Natchpai/BeyondCMoy/Beyond_CMoy/Images/Components/RK097GS.png

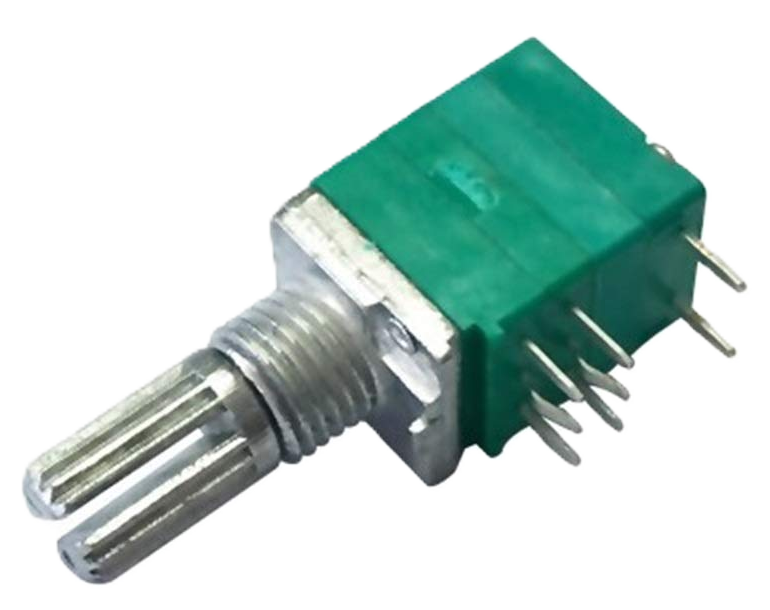
Beyond_CMoy/Images/Components/RK097GS.png
