Natchpai/BeyondCMoy/Beyond_CMoy/Images/Components/TYPEC6P019.jpg

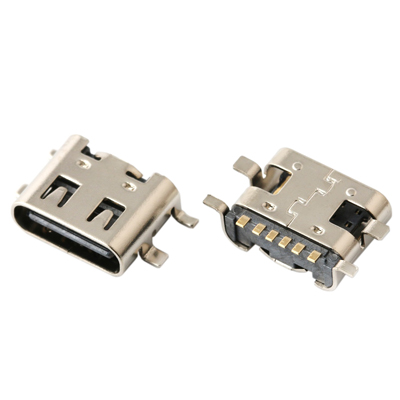
Beyond_CMoy/Images/Components/TYPEC6P019.jpg
